UBC-Solar/Legacy-array-supervisor-board/3D Models/ESQ-119-24-T-D.stp

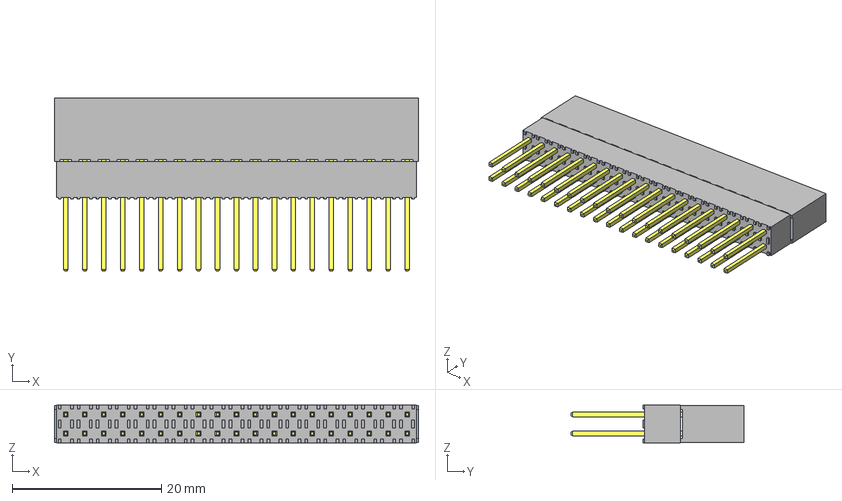
[picture p15: CAD file, 2019-04-06]
3D Models/ESQ-119-24-T-D.stp
48.8 x 23.2 x 5.08 mm
_ESQ-119-24-T-D_socket
_ESQ-119-24-T-D_pins
_ESQ-119-24-G-D-LL_bpins
