UBC-Solar/Legacy-array-supervisor-board/3D Models/SOIC08 narrow.stp

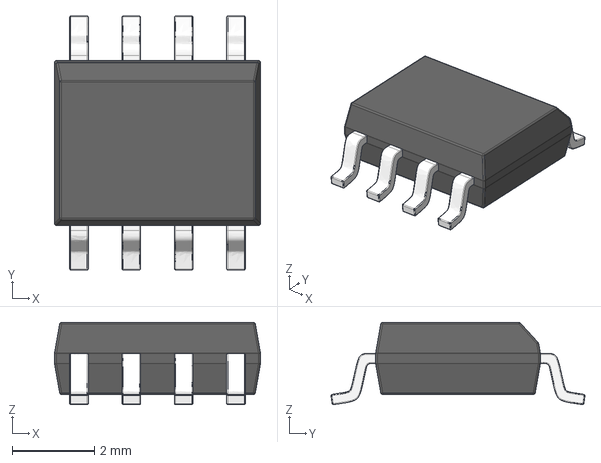
[picture p16: CAD file, 2019-04-06]
3D Models/SOIC08 narrow.stp
5.00 x 6.16 x 2.00 mm
