UBC-Solar/Legacy-array-supervisor-board/3D Models/CAPC-0805-T0.95-BN.stp

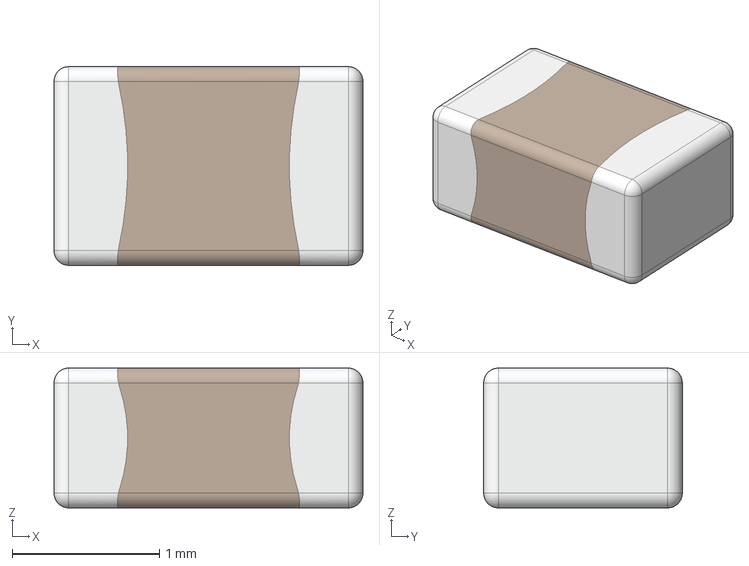
[picture p17: CAD file, 2019-03-16]
3D Models/CAPC-0805-T0.95-BN.stp
2.10 x 1.35 x 0.95 mm
