UBC-Solar/Legacy-array-supervisor-board/3D Models/RESC-0805.stp

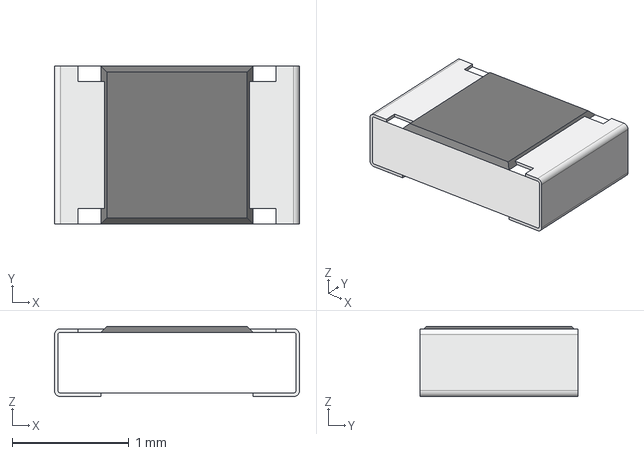
[picture p18: CAD file, 2019-03-02]
3D Models/RESC-0805.stp
2.10 x 1.35 x 0.6 mm
