UBC-Solar/Legacy-array-supervisor-board/3D Models/CAPC-0805-T1.35-BN.stp

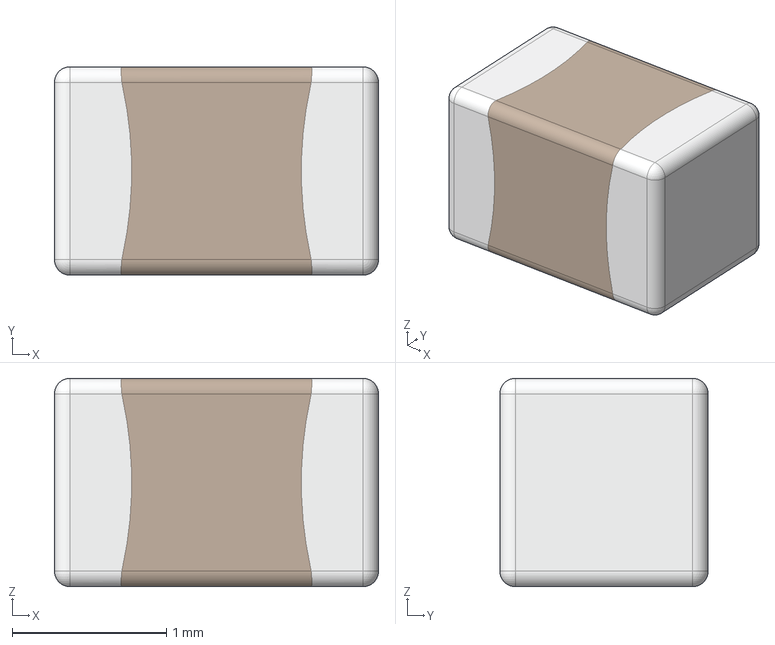
[picture p19: CAD file, 2019-03-02]
3D Models/CAPC-0805-T1.35-BN.stp
2.10 x 1.35 x 1.35 mm
