UBC-Solar/Legacy-array-supervisor-board/Voltage Sense Unit/Simulation/Voltage Sense Diff Amp_LPF.asc

C1: cap; 353.7nF
C2: cap; 353.7nF
R1: res; 20k
R2: res; 20k
R3: res; 6.2k
R4: res; 6.2k
R5: res; 9k
R6: res; 1k
R7: res; 9k
R8: res; 1k
U1: LT1677
V1: voltage; 12
V2: voltage; 100
Named nets: 0, Vout
.dc V2 0 100 1
