UBC-Solar/Legacy-array-supervisor-board/Firmwarev1/STM32Final2/Peripherals/CAN/CAN.c

/**
 * Function implementations for enabling and using CAN messaging.
 */
#include "CAN.h"

/**
 * Initializes the CAN controller with bit rate of [].
 */
 void CANInit(void)
 {
	RCC->APB1ENR |= 0x2000000UL;  // Enable CAN clock 
	RCC->APB2ENR |= 0x1UL;				 // Enable AFIO clock
	AFIO->MAPR   &= 0xFFFF9FFF;   // reset CAN remap
	AFIO->MAPR   |= 0x00004000;   //   set CAN remap, use PB8, PB9
 
	RCC->APB2ENR |= 0x8UL;				// Enable GPIOB clock
	GPIOB->CRH   &= ~(0xFFUL);
	GPIOB->CRH   |= 0xB8UL;			// Configure PB8 and PB9
	GPIOB->ODR |= 0x1UL << 8;
  
	CAN1->MCR     = 0x11UL;      // Set CAN to initialization mode
	 
	// Set bit rates 
	CAN1->BTR &= ~(((0x03) << 24) | ((0x07) << 20) | ((0x0F) << 16) | (0x1FF)); 
	CAN1->BTR |=  (((2-1) & 0x07) << 20) | (((15-1) & 0x0F) << 16) | ((2-1) & 0x1FF);
 

	// Configure Filters
	CAN1->FMR  |=   0x1UL;                // Set to filter initialization mode
	CAN1->FA1R &= ~(0x1UL);               // Deactivate filter 0
	CAN1->FS1R |=   0x1UL;                // Set first filter to single 32 bit configuration
 
	CAN1->sFilterRegister[0].FR1 = 0x0UL; // Set filter registers to 0
	CAN1->sFilterRegister[0].FR2 = 0x0UL; // Set filter registers to 0
	CAN1->FM1R &= ~(0x1UL);               // Set filter to mask mode
 
	CAN1->FFA1R &= ~(0x1UL);			  // Apply filter to FIFO 0  
	CAN1->FA1R  |=   0x1UL;               // Activate filter 0
	
	CAN1->FMR   &= ~(0x1UL);			  // Deactivate initialization mode
	CAN1->MCR   &= ~(0x1UL);              // Set CAN to normal mode 
	while (CAN1->MSR & 0x1UL); 
 
 }
 
/**
 * Decodes CAN messages from the data registers and populates a 
 * CAN message struct with the data fields.
 * 
 * @preconditions A valid CAN message is received
 * @params CAN_rx_msg - CAN message struct that will be populated
 * 
 */
 void CANReceive(CAN_msg_t* CAN_rx_msg)
 {
	CAN_rx_msg->id  = (CAN1->sFIFOMailBox[0].RIR >> 21) & 0x7FFUL;
	CAN_rx_msg->len = (CAN1->sFIFOMailBox[0].RDTR) & 0xFUL;
	
	CAN_rx_msg->data[0] = 0xFFUL &  CAN1->sFIFOMailBox[0].RDLR;
	CAN_rx_msg->data[1] = 0xFFUL & (CAN1->sFIFOMailBox[0].RDLR >> 8);
	CAN_rx_msg->data[2] = 0xFFUL & (CAN1->sFIFOMailBox[0].RDLR >> 16);
	CAN_rx_msg->data[3] = 0xFFUL & (CAN1->sFIFOMailBox[0].RDLR >> 24);
	CAN_rx_msg->data[4] = 0xFFUL &  CAN1->sFIFOMailBox[0].RDHR;
	CAN_rx_msg->data[5] = 0xFFUL & (CAN1->sFIFOMailBox[0].RDHR >> 8);
	CAN_rx_msg->data[6] = 0xFFUL & (CAN1->sFIFOMailBox[0].RDHR >> 16);
	CAN_rx_msg->data[7] = 0xFFUL & (CAN1->sFIFOMailBox[0].RDHR >> 24);
	
	CAN1->RF0R |= 0x20UL;
 }
 
/**
 * Encodes CAN messages using the CAN message struct and populates the 
 * data registers with the sent.
 * 
 * @preconditions A valid CAN message is received
 * @params CAN_rx_msg - CAN message struct that will be populated
 * 
 */
 void CANSend(CAN_msg_t* CAN_tx_msg)
 {
	CAN1->sTxMailBox[0].TIR   = (CAN_tx_msg->id) << 21;
	
	CAN1->sTxMailBox[0].TDTR &= ~(0xF);
	CAN1->sTxMailBox[0].TDTR |= CAN_tx_msg->len & 0xFUL;
	
	CAN1->sTxMailBox[0].TDLR  = (((uint32_t) CAN_tx_msg->data[3] << 24) |
								 ((uint32_t) CAN_tx_msg->data[2] << 16) |
								 ((uint32_t) CAN_tx_msg->data[1] <<  8) |
								 ((uint32_t) CAN_tx_msg->data[0]      ));
	CAN1->sTxMailBox[0].TDHR  = (((uint32_t) CAN_tx_msg->data[7] << 24) |
								 ((uint32_t) CAN_tx_msg->data[6] << 16) |
								 ((uint32_t) CAN_tx_msg->data[5] <<  8) |
								 ((uint32_t) CAN_tx_msg->data[4]      ));

	CAN1->sTxMailBox[0].TIR  |= 0x1UL;
	while(CAN1->sTxMailBox[0].TIR & 0x1UL);
 }

 /**
 * Returns whether there are CAN messages available.
 *
 * @returns If pending CAN messages are in the CAN controller
 *
 */
 uint8_t CANMsgAvail(void)
 {
	 return CAN1->RF0R & 0x3UL;
}
